180D-FW-2021/Team1/gesture/IMUpi_case_photos/IMUpi_case3.jpg

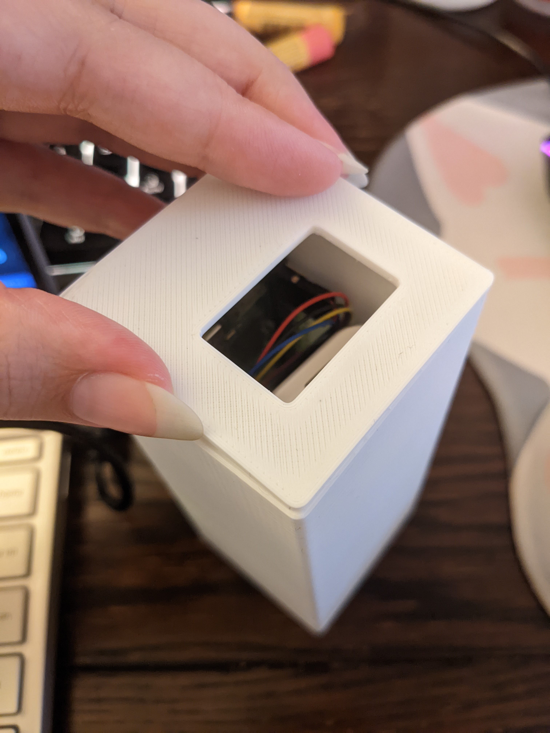
gesture/IMUpi_case_photos/IMUpi_case3.jpg
