180D-FW-2021/Team1/gesture/IMUpi_case_photos/IMUpi_case5.jpg

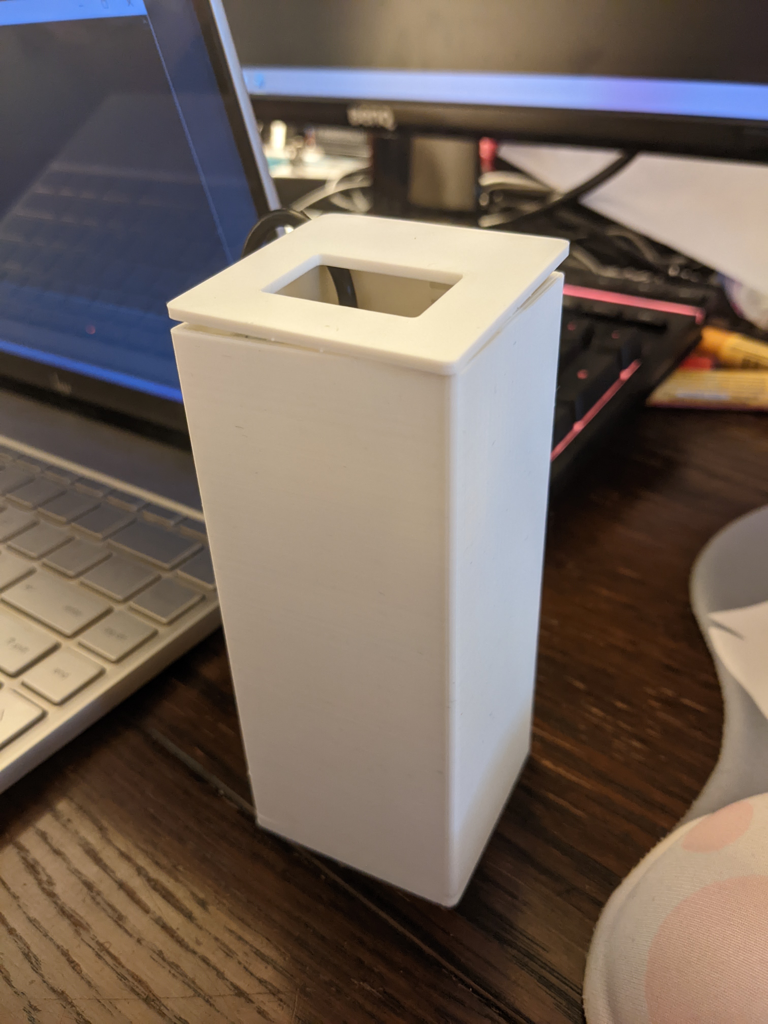
gesture/IMUpi_case_photos/IMUpi_case5.jpg
