180D-FW-2021/Team1/gui/pose_images/Hands-Together.jpg

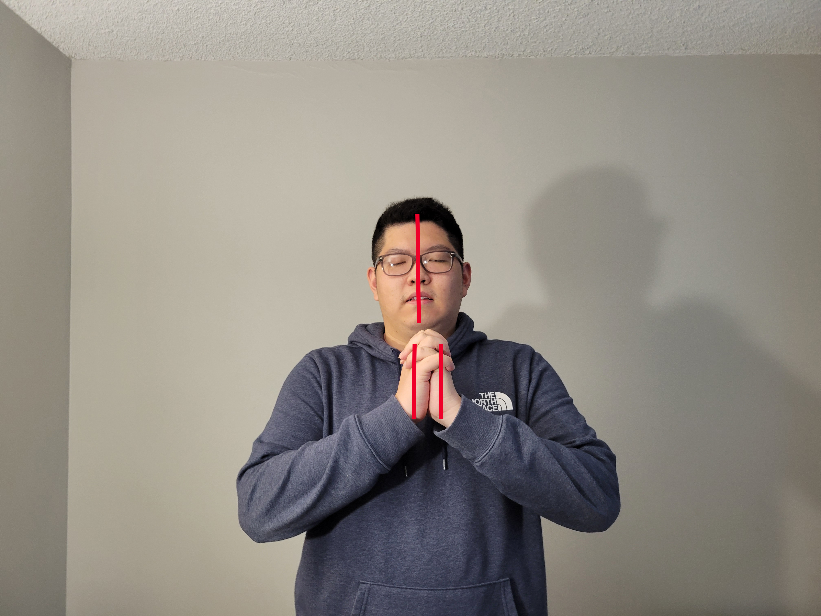
gui/pose_images/Hands-Together.jpg
