180D-FW-2021/Team1/gui/pose_images/Muscle-Man.jpg

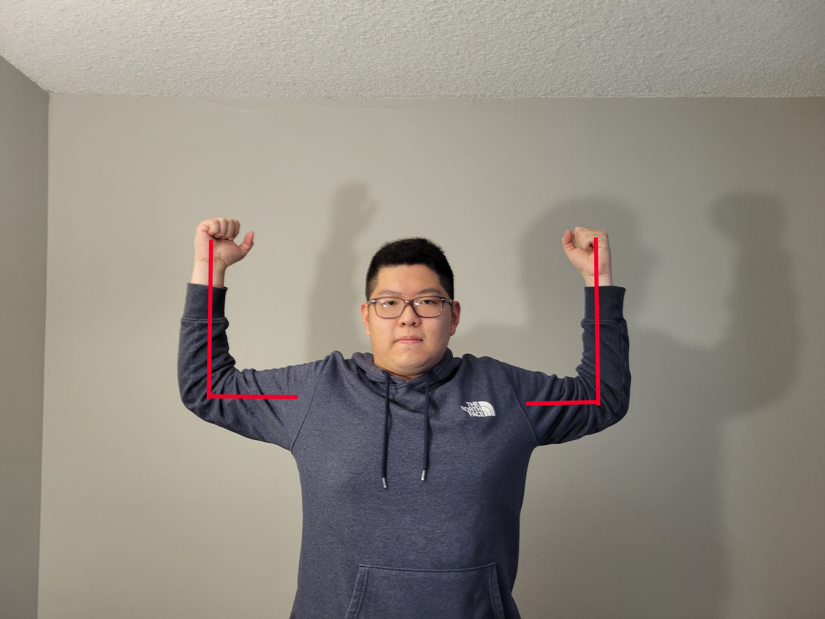
gui/pose_images/Muscle-Man.jpg
