180D-FW-2021/Team1/gui/pose_images/Owo.jpg

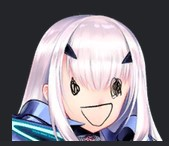
gui/pose_images/Owo.jpg
